onchipuis/mriscv/board/eagle/microAXI/PCB2-crop.pdf

## TP3 TP4 TP5 TP6 TP7 TP8

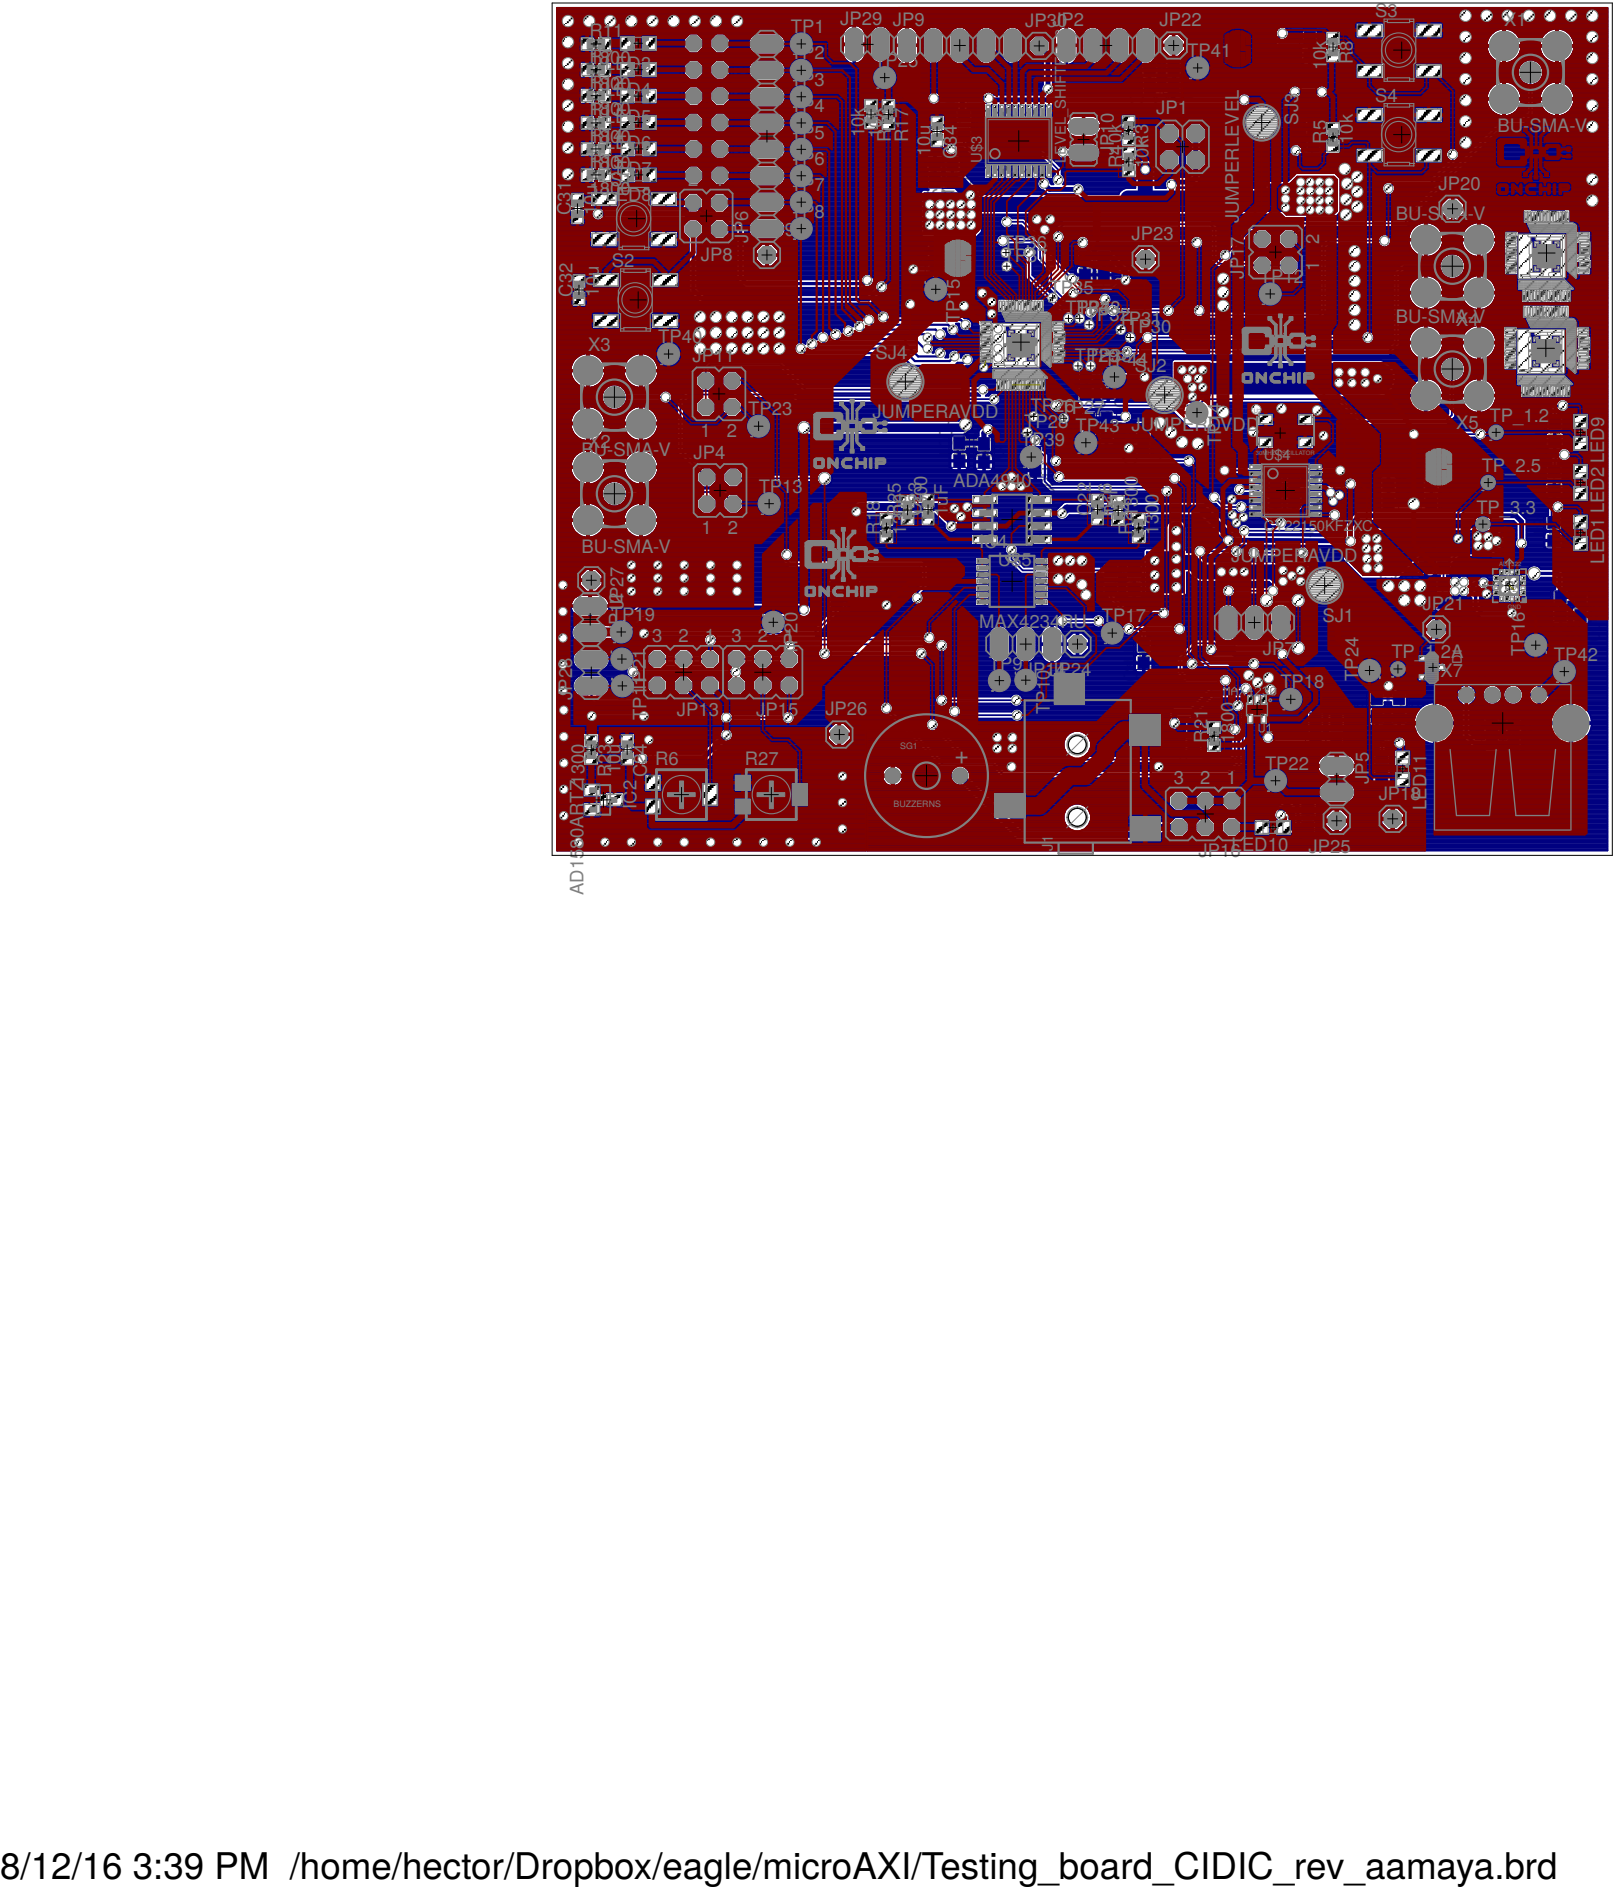
[picture p55: page 1]

8/12/16 3:39 PM /home/hector/Dropbox/eagle/microAXI/Testing_board_CIDIC_rev_aamaya.brd
