onchipuis/mriscv/board/eagle/microAXI/PCB2.pdf

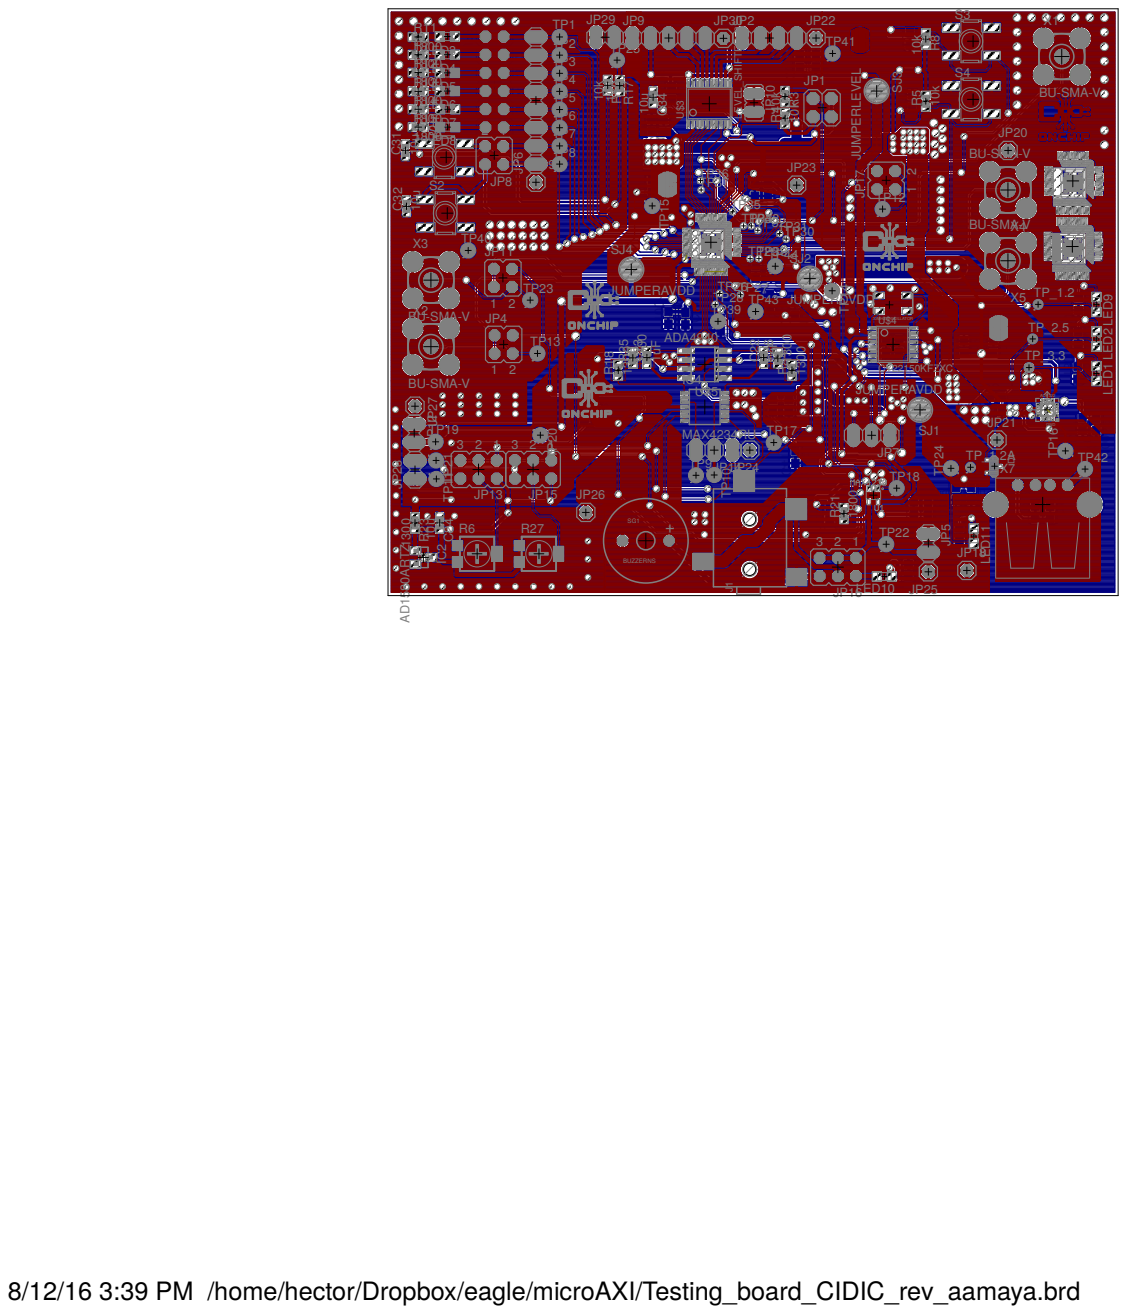
[picture p56: page 1]

8/12/16 3:39 PM /home/hector/Dropbox/eagle/microAXI/Testing_board_CIDIC_rev_aamaya.brd
